BoujeeEnjinia1701/machinepulse/cad/drawings/MPL-DWG-001.pdf

CONCEPT, NOT FOR FABRICATION | MachinePulse · github.com/BoujeeEnjinia1701/machinepulse

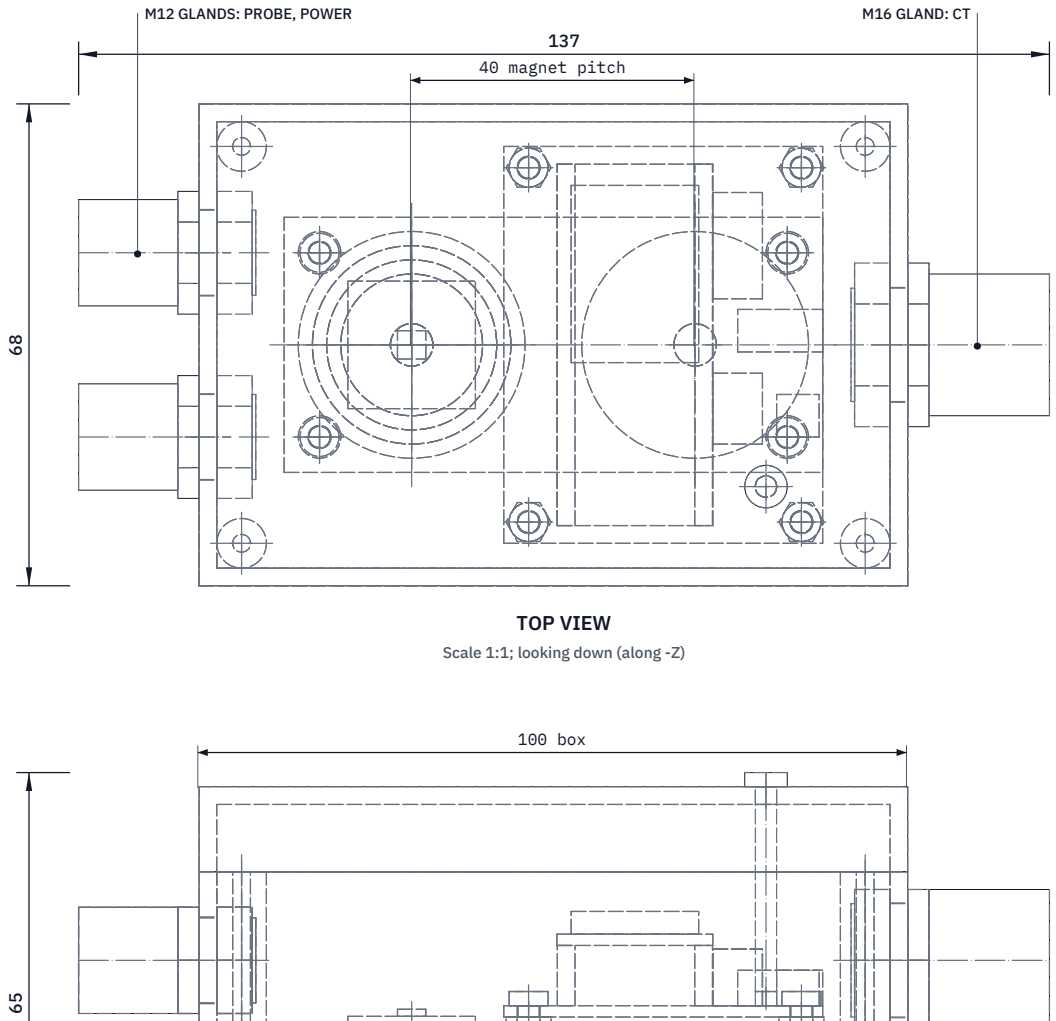
[picture p35: figure]
TOP VIEW; Scale 1:1; looking down (along -Z); 100 box; 40 magnet pitch; M12 GLANDS: PROBE, POWER; M16 GLAND: CT
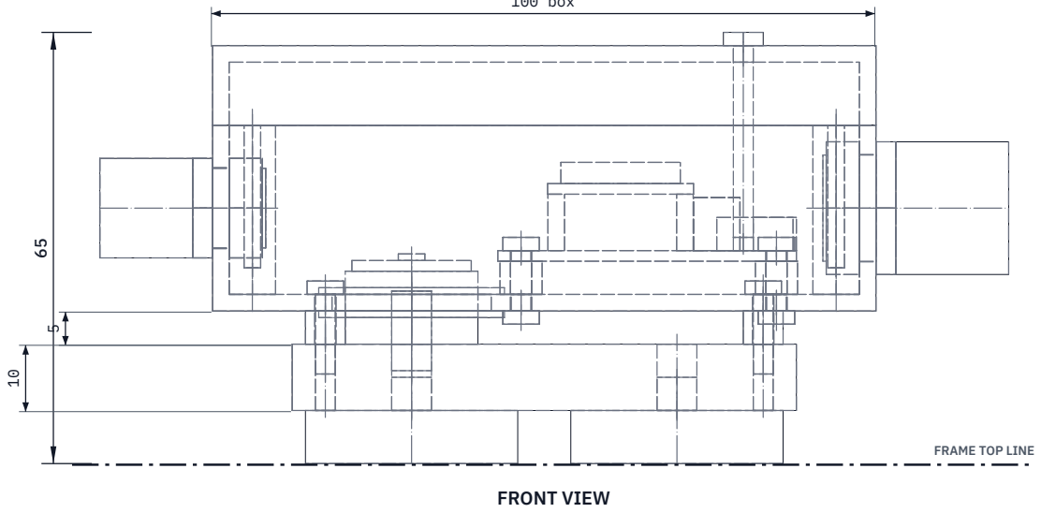
[picture p36: figure]
FRONT VIEW; FRAME TOP LINE

Scale 1:1; looking at the front (along +Y)

RIGHT VIEW
Scale 1:1; looking at the right side (along -X)

40 box

63 overall

8

ACCELEROMETER ON D20 BOSS

ISOMETRIC VIEW, INSTALLED
Not to scale; motor grey context, not in the BOM; seen from the front right and above, about 30 deg elevation

MAIN DIMENSIONS AND INTERFACES (MM)
Pod 100 x 68 x 63 high from magnet face; 137 over glands
Two D32 pot magnets rated 120 °C, M6 studs, 40 pitch
Block 76 x 36 x 10 plate; boss D20 x 11 on an M6 set screw, through D24 Four nylon stand-offs D6 x 5; silicone grommet seals the boss
IP54 ABS box, base 28 + lid 12; carrier board on 5 stand-offs
CT SCT-013 class, D13 aperture, one insulated conductor
Probe: DS18B20 sleeve D6 held on its pad by a made magnetic clip Power: certified 5 V USB adapter, 2 m lead; 0.42 W (MPL-CAL-001) Third-angle; front view from -Y; X along the motor shaft
REV | DESCRIPTION | DATE | BY
P1 | Preliminary GA for TRL 3 (from cad/src/model.py) | 2026-09-25 | AC
P2 | High-temperature magnets per MPL-DDR-002 | 2026-09-25 | AC
P3 | Layout and labels tidied | 2026-09-30 | AC
P4 | Constructable design per MPL-DDR-003: boss, glands, grommet, carrier board | 2026-10-01 | AC
MACHINEPULSE | github.com/BoujeeEnjinia1701/machinepulse

## General arrangement

DRAWING NO.
MPL-DWG-001

REV
P4

SHEET
1 of 1

SIZE

## ANSI B

SCALE
1:1

UNITS
mm
PROJECTION | DATE
2026-10-01

DRAWN
Amish Chadha

MATERIAL / NOTES
ABS box, 6061 block, nylon stand-offs; bought-in parts per bom/bom.csv. PRELIMINARY, NOT FOR FABRICATION
Licensed CERN-OHL-S-2.0 · Design Molecule Lab · designmolecule.com | Generated from cad/src; do not edit by hand
