BoujeeEnjinia1701/machinepulse/cad/drawings/MPL-DWG-101.pdf

BUILD PLAN SKETCH, PLAN NOT YET BUILT MachinePulse · github.com/BoujeeEnjinia1701/machinepulse

FRONT VIEW
Scale 1:1; looking at the front (along +Y)

TOP VIEW
Scale 1:1; looking down (along -Z)

RIGHT VIEW
Scale 1:1; looking at the right side (along -X)

76

36 10

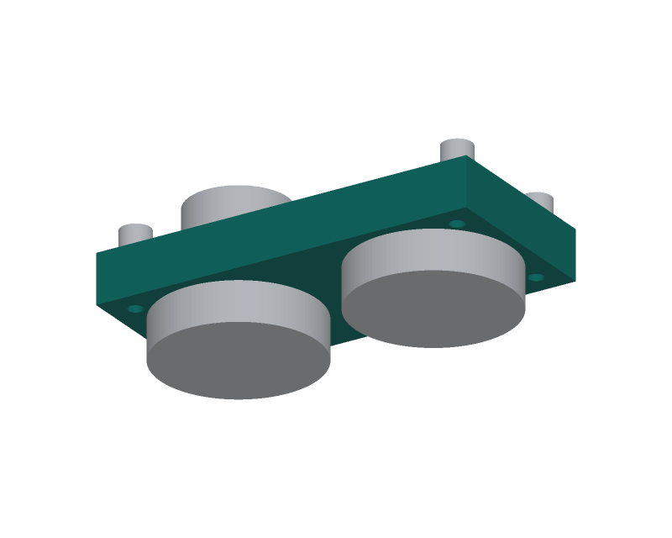
[picture p37: figure]

WHERE IT GOES
This part in colour, its neighbours in grey

HOW TO MAKE IT AND HOW IT FITS
Cut a 76 x 36 mm blank from 10 mm aluminium plate; file the
edges square and flat. Front view: the long face; top: the top face. Mark a centre line both ways. Sizes are from those centre lines. Magnet holes: two, 20 mm each side of centre on the long centre line. Drill 5.0 mm through and tap M6 through. The left one (boss end) also takes the boss's set screw from the top.
Stand-off holes: four, 33 mm each side and 13 mm each side.
Drill 2.5 mm through and tap M3 through.
Use a drill press so the holes are square to the faces.
Deburr; the top face must stay flat: the boss and stand-offs sit on it. Fit: magnets screw in from below, the boss on top over the left magnet, the four stand-offs on top at the corners.
Check: an M6 screw turns in both holes by hand, square to the face.
REV | DESCRIPTION | DATE | BY
P1 | Making sketch for the prototype build plan | 2026-10-01 | AC
MACHINEPULSE | github.com/BoujeeEnjinia1701/machinepulse

## MachinePulse sensor block: making sketch

DRAWING NO.
MPL-DWG-101

REV
P1

SHEET
1 of 1

SIZE

## ANSI B

SCALE
1:1

UNITS
mm
PROJECTION | DATE
2026-10-01

DRAWN
Amish Chadha

MATERIAL / NOTES
Aluminium plate 10 mm, 6061 or clean scrap
Licensed CERN-OHL-S-2.0 · Design Molecule Lab · designmolecule.com | Generated from cad/src; do not edit by hand
