BoujeeEnjinia1701/machinepulse/cad/drawings/MPL-DWG-102.pdf

BUILD PLAN SKETCH, PLAN NOT YET BUILT MachinePulse · github.com/BoujeeEnjinia1701/machinepulse

FRONT VIEW
Scale 2:1; looking at the front (along +Y)

TOP VIEW
Scale 2:1; looking down (along -Z)

RIGHT VIEW
Scale 2:1; looking at the right side (along -X)

20

20 11

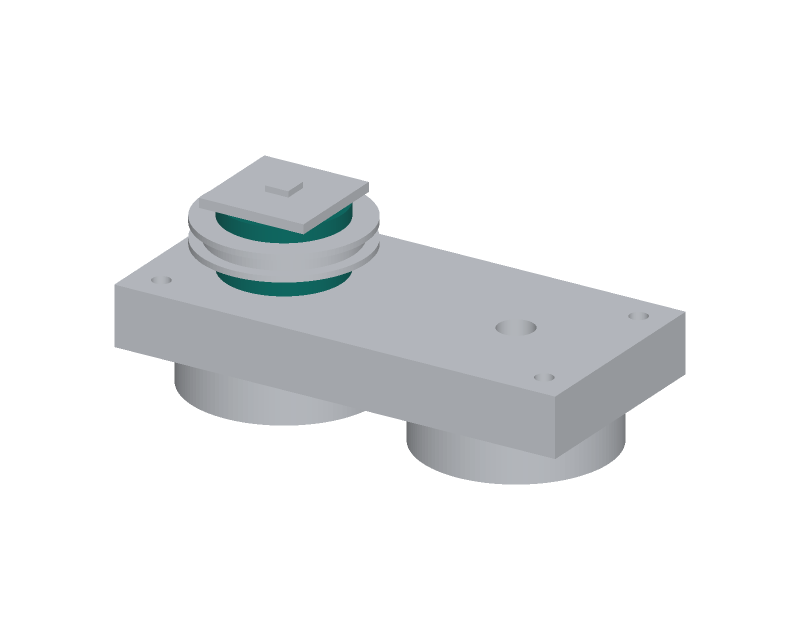
[picture p38: figure]

WHERE IT GOES
This part in colour, its neighbours in grey

HOW TO MAKE IT AND HOW IT FITS
Saw an 11 mm length off 20 mm round bar, leaving a little to file. File both ends flat and square to the bar until it is 11 mm long. Check squareness with an engineer's square on a flat plate. Centre punch the bottom end. In a drill press, with the bar held upright in a V-block, drill 5.0 mm, 8 mm deep, and tap M6 8 deep. The top end stays solid: the accelerometer board is bonded to it. Break the sharp edges lightly; do not round the top face.
Fit: an M6 x 12 set screw goes half into the block's left magnet hole and half into the boss, with medium threadlocker. Screw the boss down hard so its bottom face sits flat on the block.
The boss rises through the box floor hole and its grommet;
its top is 3.5 mm above the inside of the box floor.
Check: boss upright on the block, no rocking, top face flat.
REV | DESCRIPTION | DATE | BY
P1 | Making sketch for the prototype build plan | 2026-10-01 | AC
MACHINEPULSE | github.com/BoujeeEnjinia1701/machinepulse

## MachinePulse sensor boss: making sketch

DRAWING NO.
MPL-DWG-102

REV
P1

SHEET
1 of 1

SIZE

## ANSI B

SCALE
2:1

UNITS
mm
PROJECTION | DATE
2026-10-01

DRAWN
Amish Chadha

MATERIAL / NOTES
Aluminium round bar 20 mm, 6061 or 6082
Licensed CERN-OHL-S-2.0 · Design Molecule Lab · designmolecule.com | Generated from cad/src; do not edit by hand
