BoujeeEnjinia1701/machinepulse/cad/drawings/MPL-DWG-103.pdf

BUILD PLAN SKETCH, PLAN NOT YET BUILT MachinePulse · github.com/BoujeeEnjinia1701/machinepulse

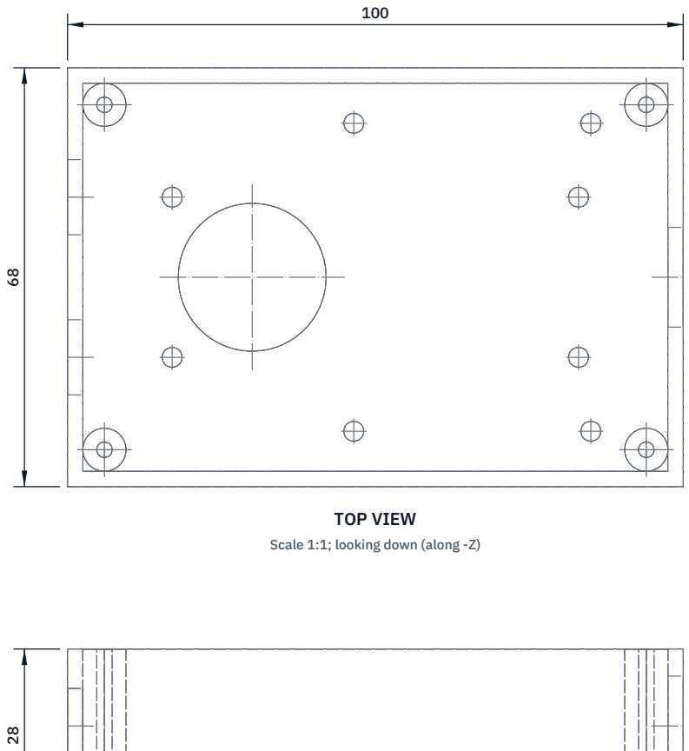
[picture p39: figure]
TOP VIEW; Scale 1:1; looking down (along -Z)

FRONT VIEW
Scale 1:1; looking at the front (along +Y)

RIGHT VIEW
Scale 1:1; looking at the right side (along -X)

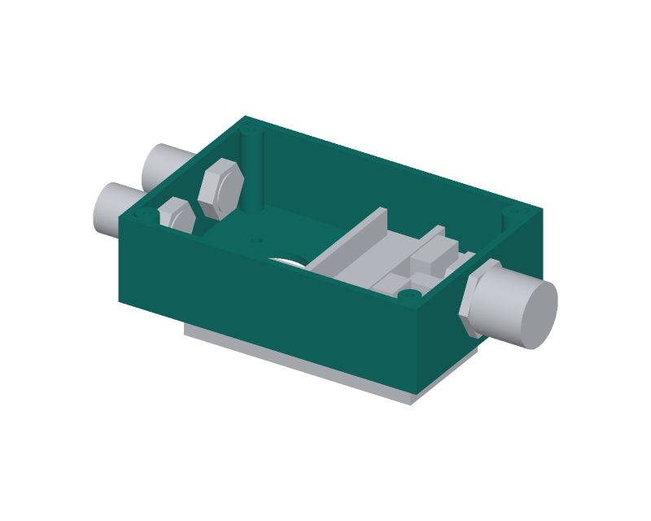
[picture p40: figure]

WHERE IT GOES
This part in colour, its neighbours in grey

HOW TO MAKE IT AND HOW IT FITS
A stock ABS box base with four moulded corner pillars. Drill only. Sizes are from the box's centre lines; the drilling layout repeats them. Floor, 24 mm boss hole: 20 mm left of centre, on the centre line. Floor, four 3.2 mm stand-off screw holes: 33 mm each side, 13 mm each side of the centre line.
Floor, four 3.2 mm carrier screw holes: 3.5 mm left of centre and 35 mm right of centre, 25 mm each side of the centre line.
Left end wall: two 12.2 mm gland holes 13 mm each side of centre. Right end wall: one 16.2 mm gland hole on the centre line.
Gland centres 15.5 mm up from the underside of the box.
Tape the face, pilot 3 mm slowly with wood behind, open with a step drill at low speed, light pressure. Deburr inside and out.
Check: each gland seats flat; the floor holes match the block's.
REV | DESCRIPTION | DATE | BY
P1 | Making sketch for the prototype build plan | 2026-10-01 | AC
MACHINEPULSE | github.com/BoujeeEnjinia1701/machinepulse

## MachinePulse box base: drilling sketch

DRAWING NO.
MPL-DWG-103

REV
P1

SHEET
1 of 1

SIZE

## ANSI B

SCALE
1:1

UNITS
mm
PROJECTION | DATE
2026-10-01

DRAWN
Amish Chadha

MATERIAL / NOTES
Bought IP54 ABS box 100 x 68 x 40 mm (base 28 mm)
Licensed CERN-OHL-S-2.0 · Design Molecule Lab · designmolecule.com | Generated from cad/src; do not edit by hand
