BoujeeEnjinia1701/machinepulse/cad/drawings/MPL-DWG-104.pdf

BUILD PLAN SKETCH, PLAN NOT YET BUILT MachinePulse · github.com/BoujeeEnjinia1701/machinepulse

FRONT VIEW
Scale 1:1; looking at the front (along +Y)

TOP VIEW
Scale 1:1; looking down (along -Z)

RIGHT VIEW
Scale 1:1; looking at the right side (along -X)

100

68 12

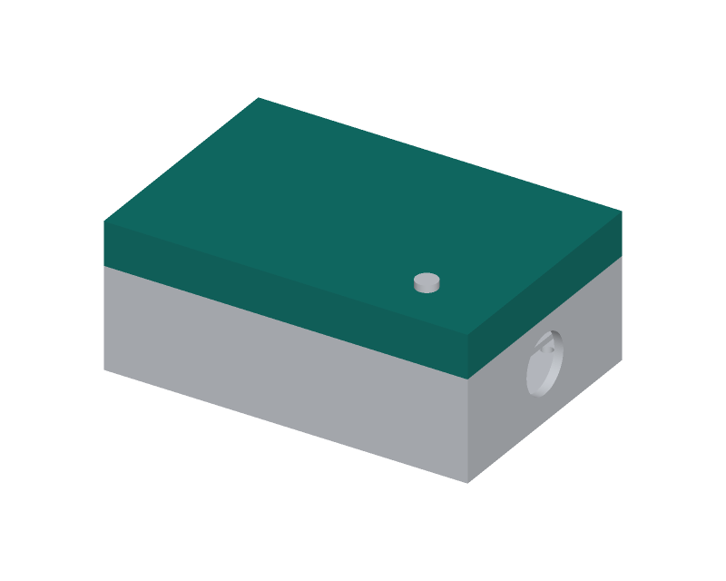
[picture p41: figure]

WHERE IT GOES
This part in colour, its neighbours in grey

HOW TO MAKE IT AND HOW IT FITS
The lid of the same stock box, with its four corner screws.
One hole for the light pipe, 3.2 mm. Mark it on the outside face: 30 mm from the centre toward the right (CT gland) end and
20 mm from the centre toward the front edge.
Drill at low speed with wood behind; deburr both faces.
Check the light pipe's datasheet: some need a 3.0 mm press-fit hole. Fit: the light pipe pushes up through the hole from inside until
its bezel sits on the lid's top face; a drop of silicone
sealant under the bezel keeps the box IP54.
The lid goes on last, its own gasket clean, with the box's four screws tightened evenly in a cross pattern.
Check: the light pipe stands upright and lines up with the LED.
REV | DESCRIPTION | DATE | BY
P1 | Making sketch for the prototype build plan | 2026-10-01 | AC
MACHINEPULSE | github.com/BoujeeEnjinia1701/machinepulse

## MachinePulse lid: drilling sketch

DRAWING NO.
MPL-DWG-104

REV
P1

SHEET
1 of 1

SIZE

## ANSI B

SCALE
1:1

UNITS
mm
PROJECTION | DATE
2026-10-01

DRAWN
Amish Chadha

MATERIAL / NOTES
Lid of the bought IP54 ABS box (lid 12 mm)
Licensed CERN-OHL-S-2.0 · Design Molecule Lab · designmolecule.com | Generated from cad/src; do not edit by hand
