BoujeeEnjinia1701/machinepulse/cad/drawings/MPL-DWG-105.pdf

BUILD PLAN SKETCH, PLAN NOT YET BUILT MachinePulse · github.com/BoujeeEnjinia1701/machinepulse

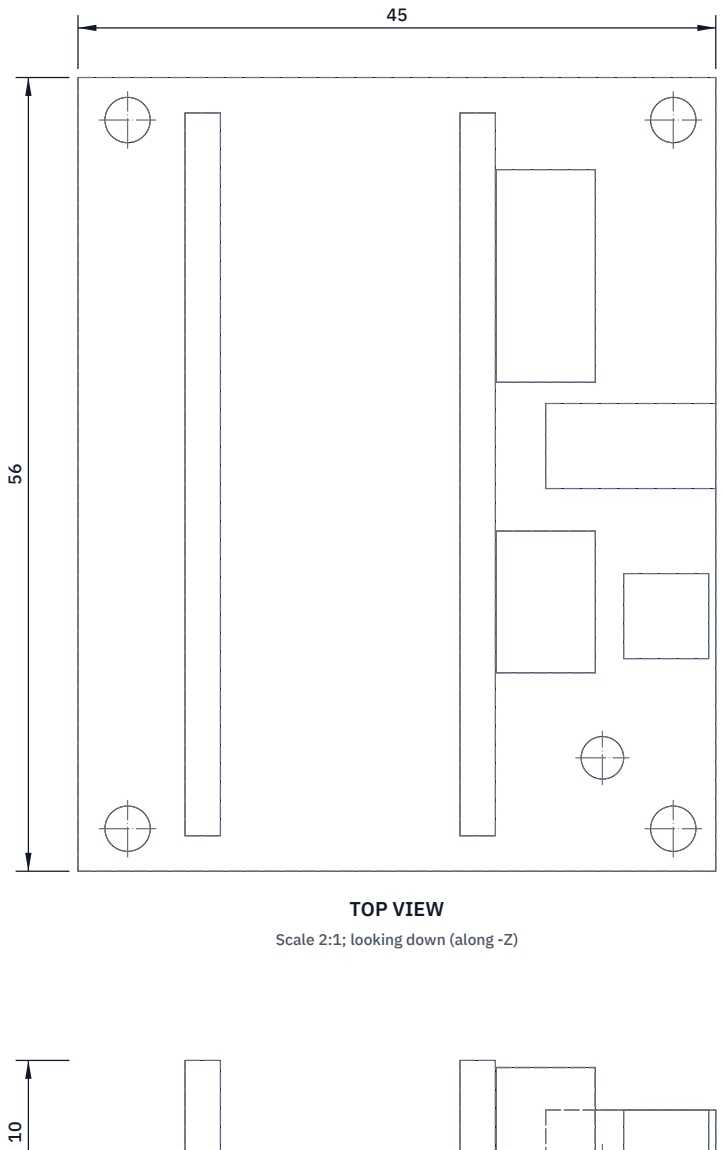
[picture p42: figure]
TOP VIEW; Scale 2:1; looking down (along -Z)

FRONT VIEW
Scale 2:1; looking at the front (along +Y)

RIGHT VIEW
Scale 2:1; looking at the right side (along -X)

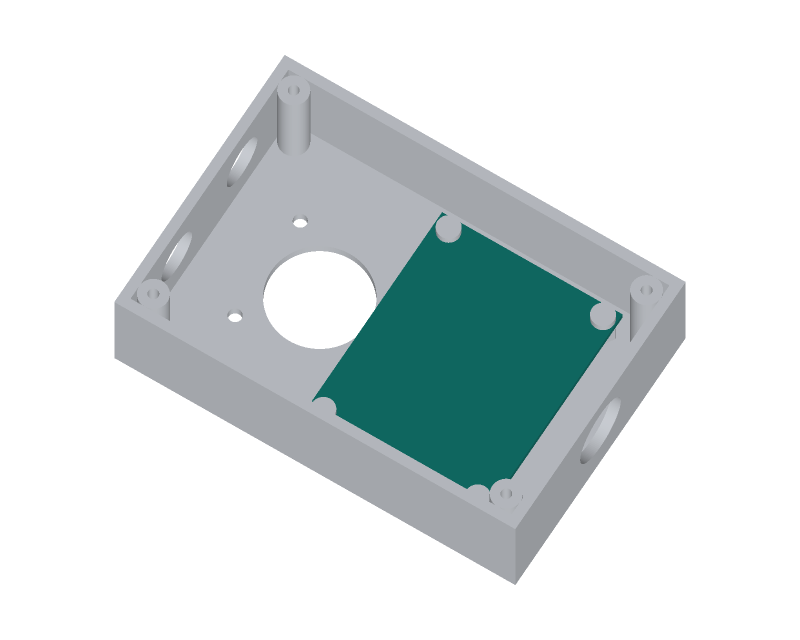
[picture p43: figure]

WHERE IT GOES
This part in colour, its neighbours in grey

HOW TO MAKE IT AND HOW IT FITS
Cut a 45 x 56 mm piece of perfboard; file the edges smooth.
Four 3.2 mm holes, 3.5 mm in from the left edge, 3 mm from the right, 3 mm in from the front and back edges (38.5 x 50 mm apart).
Left part: two 20-pin header sockets 19.4 mm apart (centre to centre), 51 mm long, for the controller board.
Right part: the 3.5 mm jack for the CT facing the right end, the 5 V and probe screw terminals, the button, and the LED 30 mm right of the box centre and 20 mm toward the front. Interface circuit as the wiring diagram: 1.50 V bias divider and filter for the CT, series resistor and clamp diodes.
Fit: on four 5 mm hex stand-offs screwed to the box floor; the board stays 4 mm clear of the right gland nut.
Check: continuity and no shorts before the controller goes in.
REV | DESCRIPTION | DATE | BY
P1 | Making sketch for the prototype build plan | 2026-10-01 | AC
MACHINEPULSE | github.com/BoujeeEnjinia1701/machinepulse

## MachinePulse carrier board: making sketch

DRAWING NO.
MPL-DWG-105

REV
P1

SHEET
1 of 1

SIZE

## ANSI B

SCALE
2:1

UNITS
mm
PROJECTION | DATE
2026-10-01

DRAWN
Amish Chadha

MATERIAL / NOTES
Perfboard 1.6 mm, 2.54 mm pitch, cut to 45 x 56 mm
Licensed CERN-OHL-S-2.0 · Design Molecule Lab · designmolecule.com | Generated from cad/src; do not edit by hand
