BoujeeEnjinia1701/machinepulse/cad/drawings/MPL-DWG-106.pdf

BUILD PLAN SKETCH, PLAN NOT YET BUILT MachinePulse · github.com/BoujeeEnjinia1701/machinepulse

FRONT VIEW
Scale 2:1; looking at the front (along +Y)

TOP VIEW
Scale 2:1; looking down (along -Z)

RIGHT VIEW
Scale 2:1; looking at the right side (along -X)

42

16 10

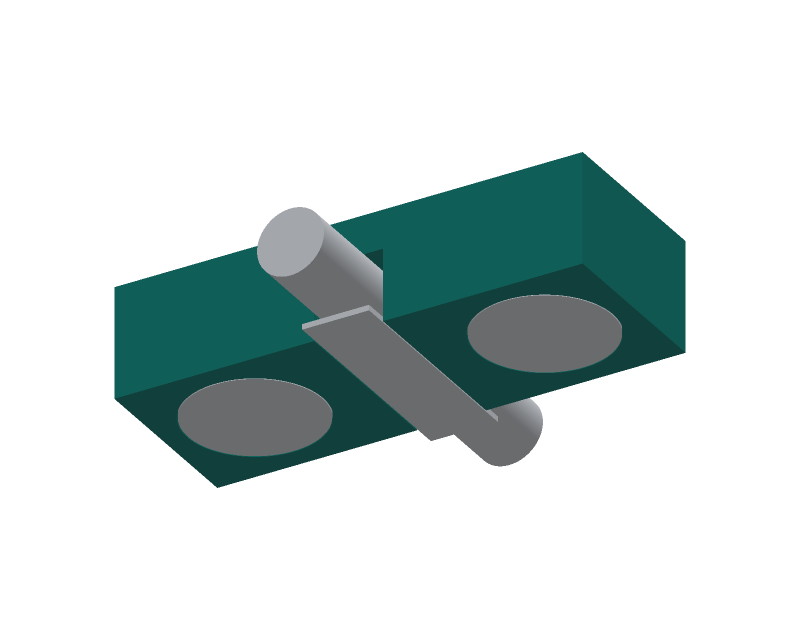
[picture p44: figure]

WHERE IT GOES
This part in colour, its neighbours in grey

HOW TO MAKE IT AND HOW IT FITS
Cut 42 mm off 16 x 10 mm bar; file the ends square.
Groove across the 16 mm width on the underside, in the middle: 6.2 mm wide, 6.5 mm deep. Saw two cuts, chisel or file out between them, and check depth with the probe sleeve and pad. Two magnet pockets on the underside, 13 mm each side of centre: 12.2 mm across, 3 mm deep, with a flat-bottomed drill or an
end mill in the drill press.
Bond a 12 x 3 mm high-temperature disc magnet in each pocket with high-temperature epoxy, flush with the underside; same pole down. Fit: the sleeve lies in the groove on its 0.5 mm thermal pad;
the magnets pull the clip onto the frame and press the sleeve
down on the pad. The lead leaves along the groove.
Check: on a steel plate the clip sits flat and the sleeve cannot slide.
REV | DESCRIPTION | DATE | BY
P1 | Making sketch for the prototype build plan | 2026-10-01 | AC
MACHINEPULSE | github.com/BoujeeEnjinia1701/machinepulse

## MachinePulse probe clip: making sketch

DRAWING NO.
MPL-DWG-106

REV
P1

SHEET
1 of 1

SIZE

## ANSI B

SCALE
2:1

UNITS
mm
PROJECTION | DATE
2026-10-01

DRAWN
Amish Chadha

MATERIAL / NOTES
Aluminium flat bar 16 x 10 mm, 6061 or 6082
Licensed CERN-OHL-S-2.0 · Design Molecule Lab · designmolecule.com | Generated from cad/src; do not edit by hand
