BoujeeEnjinia1701/machinepulse/cad/drawings/MPL-DWG-001.png

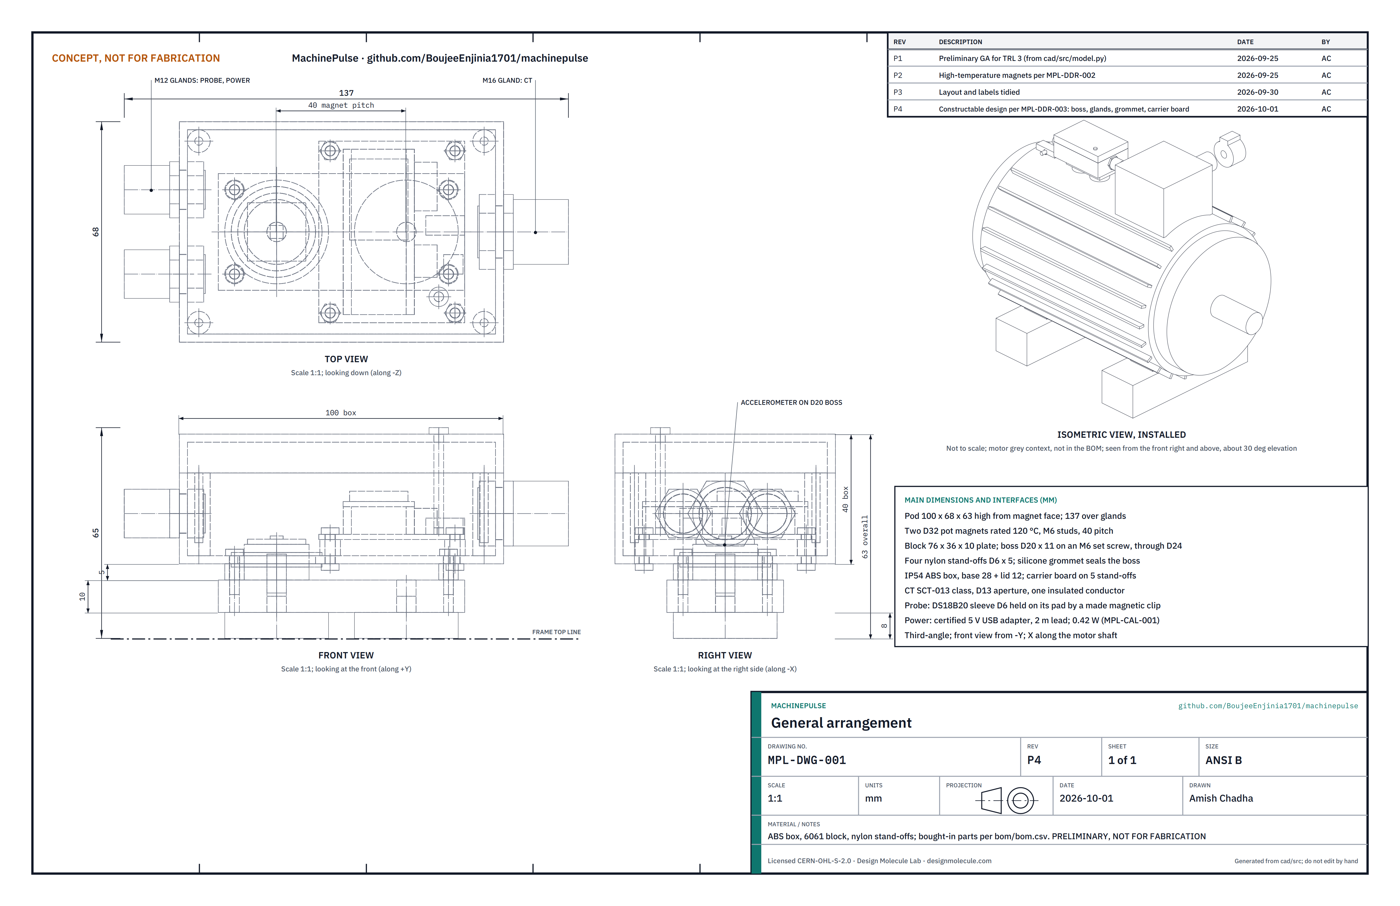
cad/drawings/MPL-DWG-001.png
