BoujeeEnjinia1701/machinepulse/media/card.png

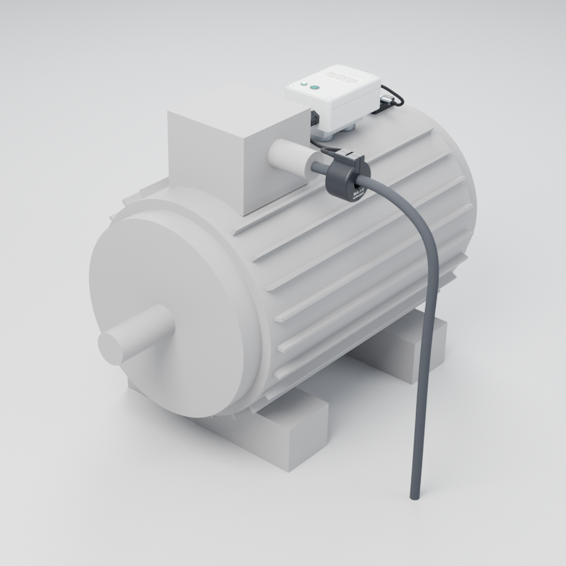
media/card.png
