BoujeeEnjinia1701/machinepulse/media/render-detail.png

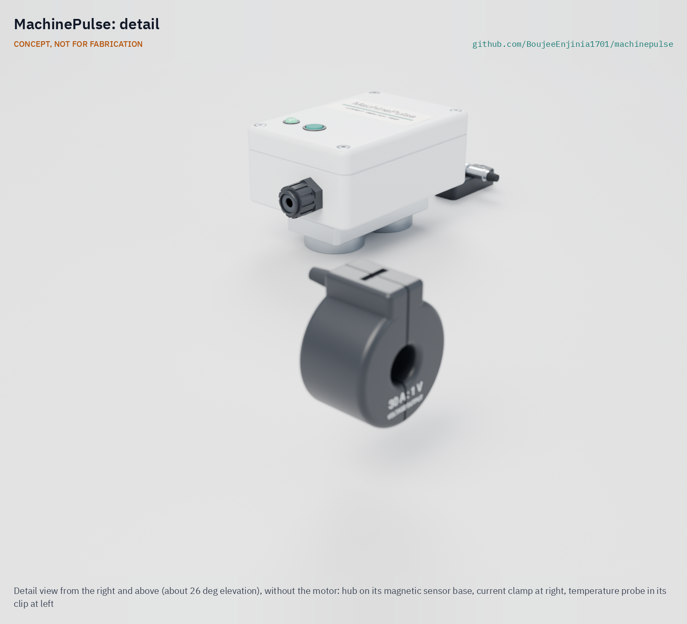
media/render-detail.png
