BoujeeEnjinia1701/machinepulse/media/render-exploded.png

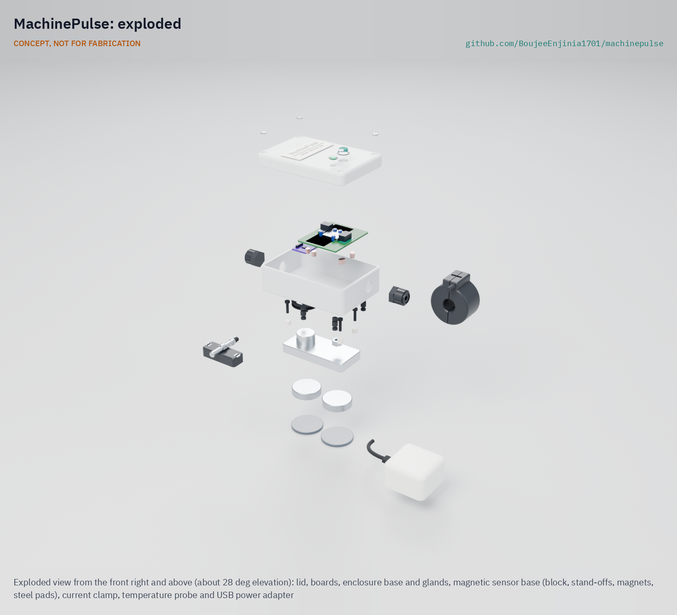
media/render-exploded.png
