BoujeeEnjinia1701/machinepulse/media/social-preview.png

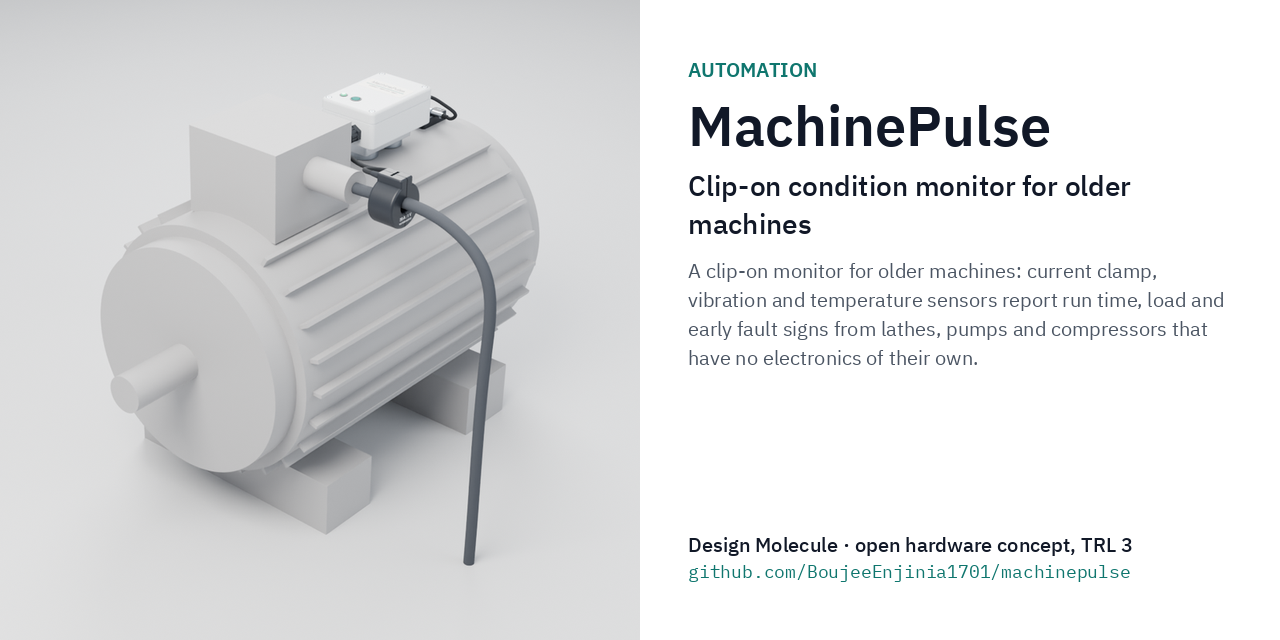
media/social-preview.png
